LJW0401/IMU_Controller/ESP32_Controller/include/wifi_param.hpp

#ifndef WIFI_PARAM_HPP
#define WIFI_PARAM_HPP
#include <Arduino.h>

extern const char * ssid;
extern const char * password;
extern const IPAddress serverIp;
extern const uint16_t serverPort;

#endif  // WIFI_PARAM_HPP
